SendorasLeft/GaiGai/lcd/asd.py

import RPI_I2C_driver
from time import *

mylcd = RPI_I2C_driver.lcd()

mylcd.lcd_clear()

# Now let's define some more custom characters
fontdata2 = [
        # Char 0 - left arrow
        [ 0x1,0x3,0x7,0xf,0xf,0x7,0x3,0x1 ],
        # Char 1 - left one bar 
        [ 0x10,0x10,0x10,0x10,0x10,0x10,0x10,0x10 ],
        # Char 2 - left two bars
        [ 0x18,0x18,0x18,0x18,0x18,0x18,0x18,0x18 ],
        # Char 3 - left 3 bars
        [ 0x1c,0x1c,0x1c,0x1c,0x1c,0x1c,0x1c,0x1c ],
        # Char 4 - left 4 bars
        [ 0x1e,0x1e,0x1e,0x1e,0x1e,0x1e,0x1e,0x1e ],
        # Char 5 - left start
        [ 0x0,0x1,0x3,0x7,0xf,0x1f,0x1f,0x1f ],
        # Char 6 - 
        # [ ],
]

# ni hao ping dao
ni = [
        # [ 0x2, 0x4, 0xd, 0x14, 0x5, 0x4, 0x4, 0x4 ],
        [ 0x1, 0x2, 0x6, 0xa, 0x2, 0x2, 0x2, 0x2 ],
        # [ 0x8, 0xe, 0xa, 0x8, 0xa, 0x8, 0x18, 0x8 ]
        [ 0x4, 0xf, 0x11, 0x4, 0x15, 0x4, 0xc, 0x4 ],
        [ 0x4, 0x8, 0x11, 0x1f, 0x12, 0xc, 0xc, 0x12 ],
        [ 0xe, 0x2, 0x4, 0x1f, 0x4, 0x4, 0xc, 0x4 ],
        [ 0x2, 0xb, 0xa, 0x1f, 0x4, 0x15, 0x2, 0x4 ],
        [ 0x1f, 0x8, 0x1f, 0x15, 0x15, 0x15, 0xa, 0x15 ],
        # [ 0x5, 0x1, 0xc, 0x5, 0x5, 0x5, 0x4, 0xf ],
        [ 0x4, 0x0, 0xc, 0x4, 0x4, 0x4, 0x4, 0xf ],
        # [ 0x14, 0x1e, 0x8, 0x1e, 0xa, 0x1e, 0x0, 0x1e ]
        # [ 0xa, 0x1f, 0x4, 0x1f, 0x15, 0x1f, 0x0, 0x1f ]
        [ 0xa, 0x1f, 0x4, 0x1f, 0x11, 0x15, 0xe, 0x1f ]
]

# zai jian sheng liang (sheng liang in 4 boxes)
zaijian = [
        #[ 0x1f, 0x4, 0x1f, 0x15, 0x1f, 0x15, 0x1f, 0x11 ],
        #[ 0x1f, 0x8, 0x1f, 0x15, 0x15, 0x15, 0xa, 0x11 ],
        [ 0x0, 0x3, 0x0, 0x1, 0x0, 0x1, 0x1, 0x1 ],
        [ 0x10, 0x1e, 0x10, 0x1c, 0x0, 0x1c, 0x14, 0x14 ],
        [ 0x1, 0x3, 0x2, 0x6, 0x4, 0xc, 0x8, 0x0 ],
        [ 0x1c, 0x0, 0x0, 0x0, 0x0, 0x0, 0x0, 0x0 ],
        [ 0x1, 0x1, 0x1, 0x1, 0x1, 0x0, 0x7, 0x0 ],
        [ 0x1c, 0x4, 0x1c, 0x4, 0x1c, 0x0, 0x1f, 0x0 ],
        [ 0x1, 0x1, 0x1, 0x1, 0x0, 0x1, 0x0, 0x7 ],
        [ 0x14, 0x1c, 0x14, 0x1c, 0x10, 0x1c, 0x10, 0x1f ]
]

mylcd.lcd_load_custom_chars(zaijian)
while True:
    mylcd.lcd_display_string("Hello", 1)
    """
    # mylcd.lcd_display_string_pos(chr(0), 1, 8)
    # mylcd.lcd_display_string_pos(chr(1), 1, 10)
    mylcd.lcd_display_string_pos(chr(0), 1, 0)
    mylcd.lcd_display_string_pos(chr(1), 1, 1)
    mylcd.lcd_display_string_pos(chr(2), 2, 0)
    mylcd.lcd_display_string_pos(chr(3), 2, 1)
    mylcd.lcd_display_string_pos(chr(4), 1, 2)
    mylcd.lcd_display_string_pos(chr(5), 1, 3)
    mylcd.lcd_display_string_pos(chr(6), 2, 2)
    mylcd.lcd_display_string_pos(chr(7), 2, 3)
    """
"""
sleep(3)
mylcd.lcd_load_custom_chars(ni)
mylcd.lcd_display_string_pos(chr(0), 1, 1)
mylcd.lcd_display_string_pos(chr(1), 1, 2)
mylcd.lcd_display_string_pos(chr(2), 1, 3)
mylcd.lcd_display_string_pos(chr(3), 1, 4)
mylcd.lcd_display_string_pos(chr(4), 1, 5)
mylcd.lcd_display_string_pos(chr(5), 1, 6)
mylcd.lcd_display_string_pos(chr(6), 1, 7)
mylcd.lcd_display_string_pos(chr(7), 1, 8)
"""
